aroum/omsk/firmware/omsk_wave/src/usb/tusb_config.h

#ifndef _TUSB_CONFIG_H_
#define _TUSB_CONFIG_H_

#include "pico/stdlib.h"
#include "sw_config.h"
#include "audio.h"

#ifndef CFG_TUSB_MCU
#define CFG_TUSB_MCU OPT_MCU_RP2040
#endif
#ifndef CFG_TUSB_OS
#define CFG_TUSB_OS OPT_OS_NONE
#endif
#define CFG_TUSB_DEBUG 0

#define CFG_TUD_ENDPOINT0_SIZE 64

#ifndef CFG_TUD_ENABLED
#define CFG_TUD_ENABLED 1
#endif

#if CFG_ENABLE_USB_AUDIO
#define CFG_TUD_AUDIO  1
#else
#define CFG_TUD_AUDIO  0
#endif

#define CFG_TUD_CDC    (CFG_ENABLE_DEBUG)
#define CFG_TUD_MIDI   (CFG_ENABLE_USB_MIDI)
#define CFG_TUD_MSC    0
#define CFG_TUD_HID    0
#define CFG_TUD_VENDOR 0

#define CFG_TUD_CDC_RX_BUFSIZE 256
#define CFG_TUD_CDC_TX_BUFSIZE 256

#define CFG_TUD_MIDI_RX_BUFSIZE 512
#define CFG_TUD_MIDI_TX_BUFSIZE 128

#if CFG_ENABLE_USB_AUDIO

#define TUD_AUDIO_INTERFACE_STEREO_DESC_LEN (TUD_AUDIO_DESC_IAD_LEN\
    + TUD_AUDIO_DESC_STD_AC_LEN\
    + TUD_AUDIO_DESC_CS_AC_LEN\
    + TUD_AUDIO_DESC_CLK_SRC_LEN\
    + TUD_AUDIO_DESC_INPUT_TERM_LEN\
    + TUD_AUDIO_DESC_OUTPUT_TERM_LEN\
    + TUD_AUDIO_DESC_STD_AS_INT_LEN\
    + TUD_AUDIO_DESC_STD_AS_INT_LEN\
    + TUD_AUDIO_DESC_CS_AS_INT_LEN\
    + TUD_AUDIO_DESC_TYPE_I_FORMAT_LEN\
    + TUD_AUDIO_DESC_STD_AS_ISO_EP_LEN\
    + TUD_AUDIO_DESC_CS_AS_ISO_EP_LEN)

#define CFG_TUD_AUDIO_ENABLE_INTERRUPT_EP                    0
#define CFG_TUD_AUDIO_FUNC_1_DESC_LEN                        TUD_AUDIO_INTERFACE_STEREO_DESC_LEN
#define CFG_TUD_AUDIO_FUNC_1_N_FORMATS                       1

#define CFG_TUD_AUDIO_FUNC_1_MAX_SAMPLE_RATE                 AUDIO_SAMPLE_RATE
#define CFG_TUD_AUDIO_FUNC_1_N_CHANNELS_TX                   2
#define CFG_TUD_AUDIO_FUNC_1_N_CHANNELS_RX                   2
#define CFG_TUD_AUDIO_FUNC_1_FORMAT_1_N_BYTES_PER_SAMPLE_TX  2
#define CFG_TUD_AUDIO_FUNC_1_FORMAT_1_RESOLUTION_TX          16
#define CFG_TUD_AUDIO_FUNC_1_FORMAT_1_N_BYTES_PER_SAMPLE_RX  2
#define CFG_TUD_AUDIO_FUNC_1_FORMAT_1_RESOLUTION_RX          16

#define CFG_TUD_AUDIO_ENABLE_EP_IN                1
#define CFG_TUD_AUDIO_FUNC_1_FORMAT_1_EP_SZ_IN    TUD_AUDIO_EP_SIZE(CFG_TUD_AUDIO_FUNC_1_MAX_SAMPLE_RATE, CFG_TUD_AUDIO_FUNC_1_FORMAT_1_N_BYTES_PER_SAMPLE_TX, CFG_TUD_AUDIO_FUNC_1_N_CHANNELS_TX)
#define CFG_TUD_AUDIO_FUNC_1_EP_IN_SW_BUF_SZ      (CFG_TUD_AUDIO_FUNC_1_FORMAT_1_EP_SZ_IN*4+64)
#define CFG_TUD_AUDIO_FUNC_1_EP_IN_SZ_MAX         (CFG_TUD_AUDIO_FUNC_1_FORMAT_1_EP_SZ_IN)

#define CFG_TUD_AUDIO_ENABLE_EP_OUT               0
#define CFG_TUD_AUDIO_FUNC_1_FORMAT_1_EP_SZ_OUT   TUD_AUDIO_EP_SIZE(CFG_TUD_AUDIO_FUNC_1_MAX_SAMPLE_RATE, CFG_TUD_AUDIO_FUNC_1_FORMAT_1_N_BYTES_PER_SAMPLE_RX, CFG_TUD_AUDIO_FUNC_1_N_CHANNELS_RX)
#define CFG_TUD_AUDIO_FUNC_1_EP_OUT_SW_BUF_SZ     (CFG_TUD_AUDIO_FUNC_1_FORMAT_1_EP_SZ_OUT*4+64)
#define CFG_TUD_AUDIO_FUNC_1_EP_OUT_SZ_MAX        (CFG_TUD_AUDIO_FUNC_1_FORMAT_1_EP_SZ_OUT)

#define CFG_TUD_AUDIO_FUNC_1_N_AS_INT             2
#define CFG_TUD_AUDIO_FUNC_1_CTRL_BUF_SZ          64

#endif

#endif
