aroum/omsk/firmware/omsk_wave/src/synth/pra32-u2-common.h

#pragma once
#include <stddef.h>
#include <stdint.h>

const int8_t FILTER_TABLE_FRACTION_BITS = 30;


#define INLINE inline __attribute__((always_inline))

static INLINE uint8_t low_byte(uint16_t x) { return x & 0xFF; }

static INLINE uint8_t high_byte(uint16_t x) { return (x >> 8) & 0xFF; }

static INLINE int32_t multiply_shift_right(int32_t x, int32_t y, uint8_t z) {
  return static_cast<int32_t>((static_cast<int64_t>(x) * y) >> z);
}

static INLINE int32_t minimum(int32_t value_0, int32_t value_1) {
  volatile int32_t result =
      (value_0 < value_1) * value_0 + (value_0 >= value_1) * value_1;
  return result;
}

static INLINE int32_t maximum(int32_t value_0, int32_t value_1) {
  volatile int32_t result =
      (value_0 > value_1) * value_0 + (value_0 <= value_1) * value_1;
  return result;
}

static INLINE int32_t clamp(int32_t value, int32_t minimum_value,
                            int32_t maximum_value) {
  volatile int32_t result =
      (value > maximum_value) * maximum_value +
      (value < minimum_value) * minimum_value +
      ((value <= maximum_value) && (value >= minimum_value)) * value;
  return result;
}
