aroum/omsk/firmware/omsk_fm/src/midi/midi_handler.h

#ifndef MIDI_HANDLER_H
#define MIDI_HANDLER_H

#include <stdint.h>

void midi_init(void);
void midi_poll(void);
void midi_process_byte(uint8_t b);
void midi_send_message(const uint8_t *msg, uint8_t length);

#endif // MIDI_HANDLER_H
