aroum/omsk/firmware/omsk_fm/src/ui/ui_oled.cpp

#include "ui_oled.h"
#include "../sw_config.h"
#include "../../../shared/image_logo.h"
#include "ui_logic.h"
#include "hardware/gpio.h"
#include "hardware/i2c.h"
#include "pico/stdlib.h"
#include "u8g2.h"
#include <stdio.h>
#include <string.h>
#include <math.h>
#include "../synth/synth.h"
#include "../synth/fm_synth.h"
#include "ui_state.h"

#define OLED_I2C_INST OLED_I2C
static u8g2_t g_u8g2;
static int g_oled_ready = 0;

static const char* LFO_NAMES[] = {"TRI ", "SAW+", "SAW-", "SQR ", "SIN ", "S&H "};

struct DexedOp {
  uint8_t x;
  uint8_t y;
  uint8_t link;
  uint8_t fb;
};

static void draw_algorithm_diagram(int algo, int x_start) {
  // Print "Alg: X" at the top-left (Y=6)
  u8g2_SetFont(&g_u8g2, u8g2_font_4x6_tf);
  char num_str[16];
  snprintf(num_str, sizeof(num_str), "Alg: %d", algo + 1);
  u8g2_DrawStr(&g_u8g2, x_start + 2, 6, num_str);
  
  // Grid area starts at Y = 6, X = 42
  int grid_x = 42;
  int grid_y = 6;
  
  // Grid step sizes (5-pixel gaps between 8x9 boxes)
  int col_w = 13;
  int row_h = 14;
  
  static const DexedOp k_dexed_algos[32][6] = {
    // Alg 1 (case 0 in dexed)
    { {2, 3, 1, 0}, {2, 2, 0, 0}, {3, 3, 2, 0}, {3, 2, 0, 0}, {3, 1, 0, 0}, {3, 0, 0, 1} },
    // Alg 2
    { {2, 3, 1, 0}, {2, 2, 0, 1}, {3, 3, 2, 0}, {3, 2, 0, 0}, {3, 1, 0, 0}, {3, 0, 0, 0} },
    // Alg 3
    { {2, 3, 1, 0}, {2, 2, 0, 0}, {2, 1, 0, 0}, {3, 3, 2, 0}, {3, 2, 0, 0}, {3, 1, 0, 1} },
    // Alg 4
    { {2, 3, 1, 0}, {2, 2, 0, 0}, {2, 1, 0, 0}, {3, 3, 2, 0}, {3, 2, 0, 0}, {3, 1, 0, 2} },
    // Alg 5
    { {2, 3, 1, 0}, {2, 2, 0, 0}, {3, 3, 1, 0}, {3, 2, 0, 0}, {4, 3, 2, 0}, {4, 2, 0, 1} },
    // Alg 6
    { {2, 3, 1, 0}, {2, 2, 0, 0}, {3, 3, 1, 0}, {3, 2, 0, 0}, {4, 3, 2, 0}, {4, 2, 0, 3} },
    // Alg 7
    { {2, 3, 1, 0}, {2, 2, 0, 0}, {3, 3, 2, 0}, {3, 2, 0, 0}, {4, 2, 7, 0}, {4, 1, 0, 1} },
    // Alg 8
    { {2, 3, 1, 0}, {2, 2, 0, 0}, {3, 3, 2, 0}, {3, 2, 0, 4}, {4, 2, 7, 0}, {4, 1, 0, 0} },
    // Alg 9
    { {2, 3, 1, 0}, {2, 2, 0, 1}, {3, 3, 2, 0}, {3, 2, 0, 0}, {4, 2, 7, 0}, {4, 1, 0, 0} },
    // Alg 10
    { {3, 3, 2, 0}, {3, 2, 0, 0}, {3, 1, 0, 1}, {2, 3, 1, 0}, {1, 2, 1, 0}, {2, 2, 0, 0} },
    // Alg 11
    { {3, 3, 2, 0}, {3, 2, 0, 0}, {3, 1, 0, 0}, {2, 3, 1, 0}, {1, 2, 1, 0}, {2, 2, 0, 1} },
    // Alg 12
    { {4, 3, 2, 0}, {4, 2, 0, 1}, {2, 3, 6, 0}, {1, 2, 1, 0}, {2, 2, 0, 0}, {3, 2, 7, 0} },
    // Alg 13
    { {4, 3, 2, 0}, {4, 2, 0, 0}, {2, 3, 6, 0}, {1, 2, 1, 0}, {2, 2, 0, 0}, {3, 2, 7, 1} },
    // Alg 14
    { {2, 3, 1, 0}, {2, 2, 0, 0}, {3, 3, 2, 0}, {3, 2, 0, 0}, {3, 1, 0, 0}, {4, 1, 7, 1} },
    // Alg 15
    { {2, 3, 1, 0}, {2, 2, 0, 4}, {3, 3, 2, 0}, {3, 2, 0, 0}, {3, 1, 0, 0}, {4, 1, 7, 0} },
    // Alg 16
    { {3, 3, 0, 0}, {2, 2, 1, 0}, {3, 2, 0, 0}, {3, 1, 0, 0}, {4, 2, 7, 0}, {4, 1, 0, 1} },
    // Alg 17
    { {3, 3, 0, 0}, {2, 2, 1, 4}, {3, 2, 0, 0}, {3, 1, 0, 0}, {4, 2, 7, 0}, {4, 1, 0, 0} },
    // Alg 18
    { {3, 3, 0, 0}, {2, 2, 1, 0}, {3, 2, 0, 4}, {4, 2, 7, 0}, {4, 1, 0, 0}, {4, 0, 0, 0} },
    // Alg 19
    { {2, 3, 1, 0}, {2, 2, 0, 0}, {2, 1, 0, 0}, {3, 3, 1, 0}, {4, 3, 2, 0}, {3, 2, 3, 1} },
    // Alg 20
    { {1, 3, 1, 0}, {2, 3, 6, 0}, {1, 2, 3, 1}, {4, 3, 2, 0}, {3, 2, 1, 0}, {4, 2, 0, 0} },
    // Alg 21
    { {1, 3, 1, 0}, {2, 3, 1, 0}, {1, 2, 3, 1}, {3, 3, 1, 0}, {4, 3, 2, 0}, {3, 2, 3, 0} },
    // Alg 22
    { {1, 3, 1, 0}, {1, 2, 0, 0}, {2, 3, 1, 0}, {3, 3, 1, 0}, {4, 3, 2, 0}, {3, 2, 4, 1} },
    // Alg 23
    { {1, 3, 1, 0}, {2, 3, 1, 0}, {2, 2, 0, 0}, {3, 3, 1, 0}, {4, 3, 2, 0}, {3, 2, 3, 1} },
    // Alg 24
    { {0, 3, 1, 0}, {1, 3, 1, 0}, {2, 3, 1, 0}, {3, 3, 1, 0}, {4, 3, 2, 0}, {3, 2, 4, 1} },
    // Alg 25
    { {0, 3, 1, 0}, {1, 3, 1, 0}, {2, 3, 1, 0}, {3, 3, 1, 0}, {4, 3, 2, 0}, {3, 2, 3, 1} },
    // Alg 26
    { {1, 3, 1, 0}, {2, 3, 6, 0}, {2, 2, 0, 0}, {4, 3, 2, 0}, {3, 2, 1, 0}, {4, 2, 0, 1} },
    // Alg 27
    { {1, 3, 1, 0}, {2, 3, 6, 0}, {2, 2, 0, 1}, {4, 3, 2, 0}, {3, 2, 1, 0}, {4, 2, 0, 0} },
    // Alg 28
    { {2, 3, 1, 0}, {2, 2, 0, 0}, {3, 3, 1, 0}, {3, 2, 0, 0}, {3, 1, 0, 1}, {4, 3, 2, 0} },
    // Alg 29
    { {1, 3, 1, 0}, {2, 3, 1, 0}, {3, 3, 1, 0}, {3, 2, 0, 0}, {4, 3, 2, 0}, {4, 2, 0, 1} },
    // Alg 30
    { {1, 3, 1, 0}, {2, 3, 1, 0}, {3, 3, 1, 0}, {3, 2, 0, 0}, {3, 1, 0, 1}, {4, 3, 2, 0} },
    // Alg 31
    { {0, 3, 1, 0}, {1, 3, 1, 0}, {2, 3, 1, 0}, {3, 3, 1, 0}, {4, 3, 2, 0}, {4, 2, 0, 1} },
    // Alg 32
    { {0, 3, 1, 0}, {1, 3, 1, 0}, {2, 3, 1, 0}, {3, 3, 1, 0}, {4, 3, 1, 0}, {5, 3, 2, 1} }
  };
  
  const DexedOp *ops = k_dexed_algos[algo < 32 ? algo : 0];
  
  // 1. Draw connection lines
  for (int op = 0; op < 6; op++) {
    const DexedOp &dop = ops[op];
    int cx = grid_x + dop.x * col_w;
    int cy = grid_y + dop.y * row_h;
    
    switch (dop.link) {
      case 0: // LINE DOWN
        u8g2_DrawVLine(&g_u8g2, cx + 4, cy + 10, (dop.y == 3) ? (63 - (cy + 10) + 1) : 5);
        break;
      case 1: // LINE RIGHT
        u8g2_DrawVLine(&g_u8g2, cx + 4, cy + 10, 3);
        u8g2_DrawHLine(&g_u8g2, cx + 4, cy + 12, col_w);
        break;
      case 2: // LINE DOWN JOIN
        u8g2_DrawVLine(&g_u8g2, cx + 4, cy + 10, (dop.y == 3) ? (63 - (cy + 10) + 1) : 3);
        break;
      case 3: // LINE RIGHT AND DOWN
        u8g2_DrawVLine(&g_u8g2, cx + 4, cy + 10, 5);
        u8g2_DrawHLine(&g_u8g2, cx + 4, cy + 12, col_w);
        u8g2_DrawVLine(&g_u8g2, cx + 4 + col_w, cy + 12, (dop.y == 3) ? (63 - (cy + 12) + 1) : 3);
        break;
      case 4: // LINE RIGHT+LEFT AND DOWN
        u8g2_DrawVLine(&g_u8g2, cx + 4, cy + 10, 5);
        u8g2_DrawHLine(&g_u8g2, cx + 4 - col_w, cy + 12, col_w * 2);
        u8g2_DrawVLine(&g_u8g2, cx + 4 + col_w, cy + 12, (dop.y == 3) ? (63 - (cy + 12) + 1) : 3);
        u8g2_DrawVLine(&g_u8g2, cx + 4 - col_w, cy + 12, (dop.y == 3) ? (63 - (cy + 12) + 1) : 3);
        break;
      case 6: // LINE RIGHT double distance
        u8g2_DrawVLine(&g_u8g2, cx + 4, cy + 10, 3);
        u8g2_DrawHLine(&g_u8g2, cx + 4, cy + 12, col_w * 2);
        break;
      case 7: // LINE LEFT
        u8g2_DrawVLine(&g_u8g2, cx + 4, cy + 10, 3);
        u8g2_DrawHLine(&g_u8g2, cx + 4 - col_w, cy + 12, col_w);
        break;
    }
  }
  
  // 2. Draw operator boxes with numbers (size 8x9)
  u8g2_SetFont(&g_u8g2, u8g2_font_4x6_tf);
  for (int op = 0; op < 6; op++) {
    const DexedOp &dop = ops[op];
    int cx = grid_x + dop.x * col_w;
    int cy = grid_y + dop.y * row_h;
    
    u8g2_SetDrawColor(&g_u8g2, 0);
    u8g2_DrawBox(&g_u8g2, cx + 1, cy + 1, 8, 9);
    u8g2_SetDrawColor(&g_u8g2, 1);
    
    u8g2_DrawFrame(&g_u8g2, cx + 1, cy + 1, 8, 9);
    
    char op_str[2] = {(char)('1' + op), '\0'};
    u8g2_DrawStr(&g_u8g2, cx + 3, cy + 8, op_str);
  }
  
  // 3. Draw feedback loops (2-pixel gap from edges)
  for (int op = 0; op < 6; op++) {
    const DexedOp &dop = ops[op];
    if (dop.fb > 0) {
      int cx = grid_x + dop.x * col_w;
      int cy = grid_y + dop.y * row_h;
      
      int y_loop_top = cy - 2;
      
      // Draw top vertical segment from top of box (cy + 1) to y_loop_top (cy - 2)
      u8g2_DrawVLine(&g_u8g2, cx + 4, y_loop_top, 3);
      
      if (dop.fb == 1) { // 1-row feedback loop on the right
        int x_loop = cx + 11;
        int y_loop_bottom = cy + 12;
        // Top horizontal segment
        u8g2_DrawHLine(&g_u8g2, cx + 4, y_loop_top, 8);
        // Right vertical segment
        u8g2_DrawVLine(&g_u8g2, x_loop, y_loop_top, y_loop_bottom - y_loop_top + 1);
        // Bottom horizontal segment
        u8g2_DrawHLine(&g_u8g2, cx + 4, y_loop_bottom, 8);
        // Bottom vertical segment touching bottom of box (cy + 9)
        u8g2_DrawVLine(&g_u8g2, cx + 4, cy + 9, 4);
      } 
      else if (dop.fb == 2 || dop.fb == 3) { // Spans to bottom of Row 3
        int x_loop = cx + 11;
        int y_loop_bottom = grid_y + 3 * row_h + 12; // Always bottom of Row 3
        // Top horizontal segment
        u8g2_DrawHLine(&g_u8g2, cx + 4, y_loop_top, 8);
        // Right vertical segment
        u8g2_DrawVLine(&g_u8g2, x_loop, y_loop_top, y_loop_bottom - y_loop_top + 1);
        // Bottom horizontal segment
        u8g2_DrawHLine(&g_u8g2, cx + 4, y_loop_bottom, 8);
        // Bottom vertical segment touching bottom of Row 3 box
        u8g2_DrawVLine(&g_u8g2, cx + 4, grid_y + 3 * row_h + 9, 4);
      } 
      else if (dop.fb == 4) { // 1-row feedback loop on the left
        int x_loop = cx - 2;
        int y_loop_bottom = cy + 12;
        // Top horizontal segment
        u8g2_DrawHLine(&g_u8g2, x_loop, y_loop_top, 7);
        // Left vertical segment
        u8g2_DrawVLine(&g_u8g2, x_loop, y_loop_top, y_loop_bottom - y_loop_top + 1);
        // Bottom horizontal segment
        u8g2_DrawHLine(&g_u8g2, x_loop, y_loop_bottom, 7);
        // Bottom vertical segment touching bottom of box (cy + 9)
        u8g2_DrawVLine(&g_u8g2, cx + 4, cy + 9, 4);
      }
    }
  }
}

static uint8_t u8x8_byte_pico_hw_i2c(u8x8_t *u8x8, uint8_t msg, uint8_t arg_int, void *arg_ptr) {
  static uint8_t buffer[1100];
  static uint16_t buf_idx;
  switch (msg) {
  case U8X8_MSG_BYTE_SEND:
    if (buf_idx + arg_int < sizeof(buffer)) {
      memcpy(buffer + buf_idx, arg_ptr, arg_int);
      buf_idx += arg_int;
    }
    break;
  case U8X8_MSG_BYTE_START_TRANSFER:
    buf_idx = 0;
    break;
  case U8X8_MSG_BYTE_END_TRANSFER: {
    uint8_t addr = u8x8_GetI2CAddress(u8x8) >> 1;
    i2c_write_timeout_us(OLED_I2C_INST, addr, buffer, buf_idx, false, 50000);
    break;
  }
  }
  return 1;
}

static uint8_t u8x8_gpio_and_delay_pico(u8x8_t *u8x8, uint8_t msg, uint8_t arg_int, void *arg_ptr) {
  switch (msg) {
  case U8X8_MSG_DELAY_MILLI:
    sleep_ms(arg_int);
    break;
  case U8X8_MSG_DELAY_10MICRO:
    sleep_us(arg_int * 10);
    break;
  case U8X8_MSG_DELAY_I2C:
    sleep_us(2);
    break;
  }
  return 1;
}

void ui_oled_init(void) {
  i2c_init(OLED_I2C_INST, 400 * 1000);
  gpio_set_function(PIN_OLED_SCL, GPIO_FUNC_I2C);
  gpio_set_function(PIN_OLED_SDA, GPIO_FUNC_I2C);
  gpio_pull_up(PIN_OLED_SCL);
  gpio_pull_up(PIN_OLED_SDA);

#if CFG_OLED_TYPE == 1
  u8g2_Setup_sh1107_i2c_64x128_f(&g_u8g2, U8G2_R1, u8x8_byte_pico_hw_i2c, u8x8_gpio_and_delay_pico);
#else
#ifdef OLED_FLIP
  u8g2_Setup_ssd1312_i2c_128x64_noname_f(&g_u8g2, U8G2_R2, u8x8_byte_pico_hw_i2c, u8x8_gpio_and_delay_pico);
#else
  u8g2_Setup_ssd1312_i2c_128x64_noname_f(&g_u8g2, U8G2_R0, u8x8_byte_pico_hw_i2c, u8x8_gpio_and_delay_pico);
#endif
#endif

  u8g2_InitDisplay(&g_u8g2);
  u8g2_SetPowerSave(&g_u8g2, 0);
  u8x8_SetI2CAddress(&g_u8g2.u8x8, 0x3C << 1);

  u8g2_ClearBuffer(&g_u8g2);
  u8g2_SetBitmapMode(&g_u8g2, 1);
  u8g2_DrawXBM(&g_u8g2, 2, 7, 125, 51, image_logo_bits);
#ifdef CFG_LOGO_SUBTITLE
  if (CFG_LOGO_SUBTITLE[0] != '\0') {
    u8g2_SetFont(&g_u8g2, u8g2_font_4x6_tr);
    u8g2_uint_t width = u8g2_GetStrWidth(&g_u8g2, CFG_LOGO_SUBTITLE);
    u8g2_DrawStr(&g_u8g2, 128 - width, 63, CFG_LOGO_SUBTITLE);
  }
#endif
  u8g2_SendBuffer(&g_u8g2);
  sleep_ms(1500);

  g_oled_ready = 1;
  ui_oled_set_brightness(OLED_BRIGHTNESS_PERCENT);
}

void ui_oled_set_power(bool on) {
  if (g_oled_ready) {
    u8g2_SetPowerSave(&g_u8g2, on ? 0 : 1);
  }
}

void ui_oled_set_brightness(uint8_t percentage) {
  if (g_oled_ready) {
    u8g2_SetContrast(&g_u8g2, (percentage * 255) / 100);
  }
}

static void draw_dashed_vline(int x, int y1, int y2) {
  for (int y = y1; y <= y2; y += 2) {
    u8g2_DrawPixel(&g_u8g2, x, y);
  }
}

static void draw_eg_graph(void) {
  FmOperatorPatch &op = g_active_patch.op[active_op];
  int x0 = 10, y0 = 42;
  int w = 24;
  u8g2_DrawHLine(&g_u8g2, 5, y0, 118);
  int x = x0;
  int last_y = y0;
  for (int i = 0; i < 4; i++) {
    int lvl = y0 - (op.levels[i] * 28 / 99);
    int next_x = x + (100 - op.rates[i]) * w / 99 + 4;
    if (next_x > 120) next_x = 120;
    u8g2_DrawLine(&g_u8g2, x, last_y, next_x, lvl);
    u8g2_DrawBox(&g_u8g2, next_x - 1, lvl - 1, 3, 3);
    x = next_x;
    last_y = lvl;
  }
}

static void draw_pitch_eg_graph(void) {
  int x0 = 10, y0 = 28;
  int w = 24;
  u8g2_DrawHLine(&g_u8g2, 5, y0, 118);
  int x = x0;
  int last_y = y0;
  for (int i = 0; i < 4; i++) {
    // Pitch EG levels are centered around 50 (0 detune)
    int lvl = y0 - ((int)g_active_patch.pitch_eg_levels[i] - 50) * 14 / 50;
    int next_x = x + (100 - g_active_patch.pitch_eg_rates[i]) * w / 99 + 4;
    if (next_x > 120) next_x = 120;
    u8g2_DrawLine(&g_u8g2, x, last_y, next_x, lvl);
    u8g2_DrawBox(&g_u8g2, next_x - 1, lvl - 1, 3, 3);
    x = next_x;
    last_y = lvl;
  }
}

static void draw_vcf_graph(void) {
  uint8_t cutoff = params.vcf1_cutoff;
  uint8_t res = params.vcf1_res;
  draw_dashed_vline(cutoff, 13, 44);
  int prev_y = -1;
  for (int x = 0; x < 128; x++) {
    int y = 28;
    if (x < cutoff) {
      if (cutoff - x < 15) {
        float dist = (15 - (cutoff - x)) / 15.0f;
        y = 28 - (int)(dist * (res * 12.0f / 127.0f));
      }
    } else {
      float dist = (x - cutoff);
      float peak = (res * 12.0f / 127.0f);
      y = 28 - (int)(peak * expf(-dist / 5.0f)) + (int)(dist * 0.5f);
    }
    if (y < 13) y = 13;
    if (y > 44) y = 44;
    if (prev_y == -1) prev_y = y;
    int ymin = (y < prev_y) ? y : prev_y;
    int h = abs(y - prev_y) + 1;
    u8g2_DrawVLine(&g_u8g2, x, ymin, h);
    prev_y = y;
  }
}

static bool ui_oled_has_graph(ModuleID m) {
  return (m == MOD_EG || m == MOD_FILT || m == MOD_PITCH_EG);
}

static void ui_oled_draw_graph(const OledPage *page) {
  // Divider
  u8g2_DrawHLine(&g_u8g2, 0, 45, 128);

  // Draw appropriate graph in Y=12..44
  if (selected_module == MOD_EG) {
    draw_eg_graph();
  } else if (selected_module == MOD_FILT) {
    draw_vcf_graph();
  } else if (selected_module == MOD_PITCH_EG) {
    draw_pitch_eg_graph();
  }

  // Draw info panel at bottom Y=46..63
  u8g2_SetFont(&g_u8g2, u8g2_font_4x6_tf);
  for (int i = 0; i < 4; i++) {
    int x_off = i * 32;
    int cx = 16 + x_off;

    if (page->knobs[i].title) {
      int tw = u8g2_GetStrWidth(&g_u8g2, page->knobs[i].title);
      u8g2_DrawStr(&g_u8g2, cx - (tw / 2), 52, page->knobs[i].title);
    }

    char buf[16];
    if (page->knobs[i].value_str[0] != '\0') {
      snprintf(buf, sizeof(buf), "%s", page->knobs[i].value_str);
    } else {
      snprintf(buf, sizeof(buf), "%d", page->knobs[i].value);
    }
    int vw = u8g2_GetStrWidth(&g_u8g2, buf);
    u8g2_DrawStr(&g_u8g2, cx - (vw / 2), 62, buf);
    if (i > 0) u8g2_DrawVLine(&g_u8g2, x_off, 46, 18);
  }
}
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
